beniroquai/Open-Oxygen-Flowsensor/PYTHON/SFM3000 vs EK-P4.png

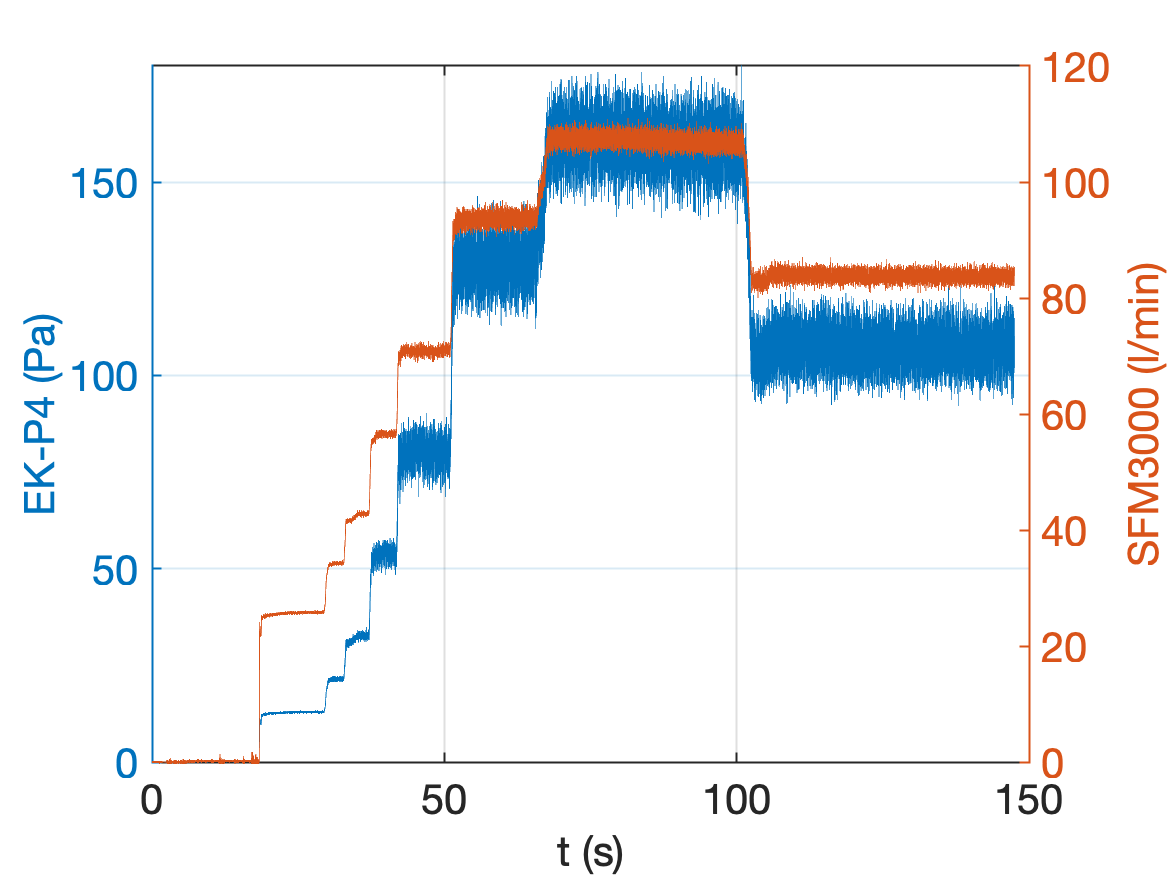
PYTHON/SFM3000 vs EK-P4.png
